jonthomasson/SolderSniffer9000/rev1.a/SolderSniffer9000.png

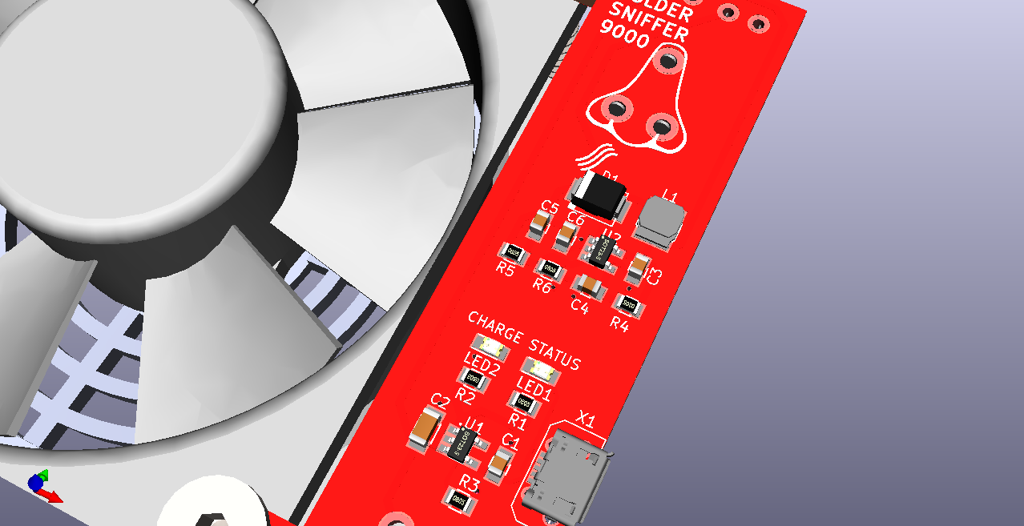
rev1.a/SolderSniffer9000.png
