jonthomasson/SolderSniffer9000/rev1.a/SolderSniffer9000_3D.png

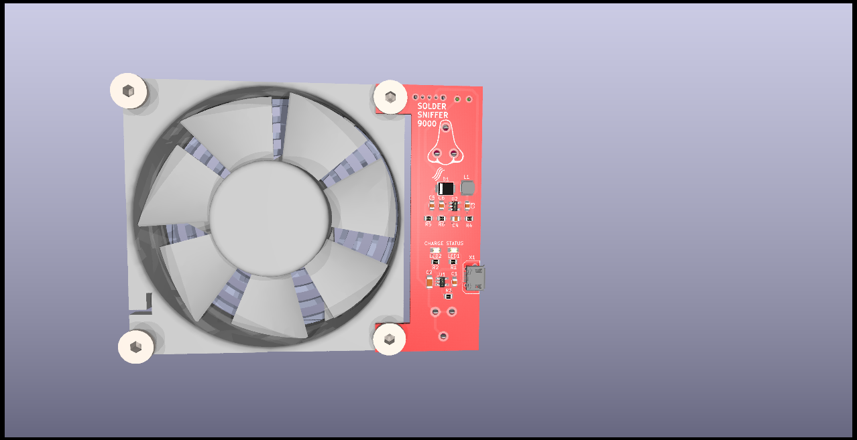
rev1.a/SolderSniffer9000_3D.png
